ARCreator0001/OneTesla-SD-Interrupter-ESP32-/ESP32InterrupterV2.0/main/midisource.h

#ifndef __MIDISOURCE_H
#define __MIDISOURCE_H
#include <SD.h>
#include "datatypes.h"

void midisource_play(const char* path, const char* title);  // play a .mid file from SD, show title on LCD

#endif
